rdalen/Boxify/KiCad/templates/Panel PCB w23.5x23.5mm/meta/panel.png

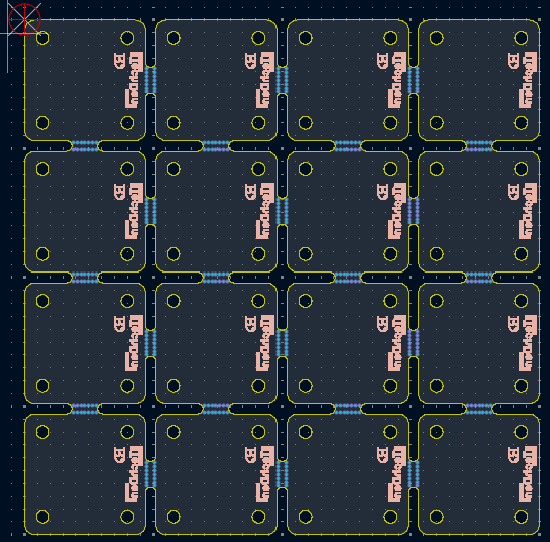
KiCad/templates/Panel PCB w23.5x23.5mm/meta/panel.png
