rdalen/Boxify/KiCad/templates/Panel PCB w23.5x49mm/meta/panel.png

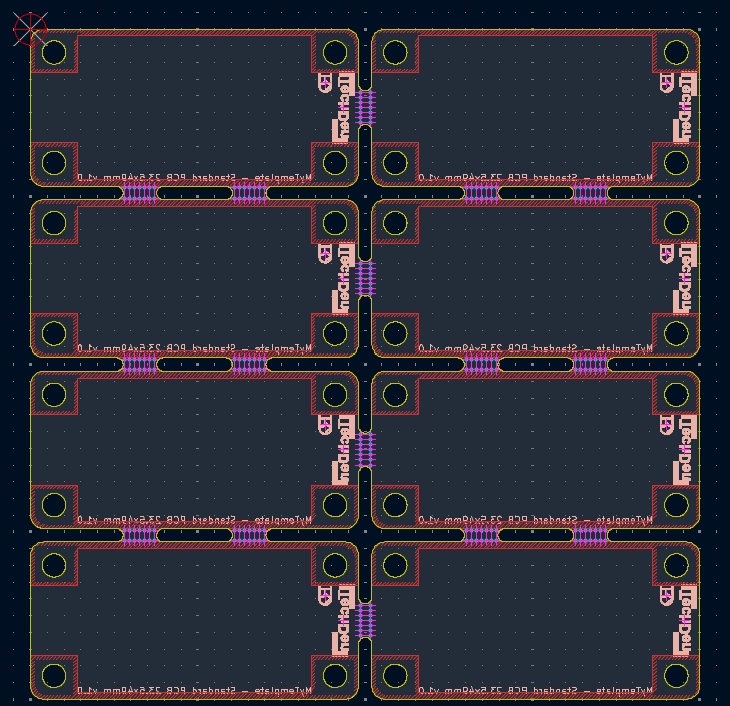
KiCad/templates/Panel PCB w23.5x49mm/meta/panel.png
