rdalen/Boxify/KiCad/templates/Panel PCB w49x49mm/meta/panel.png

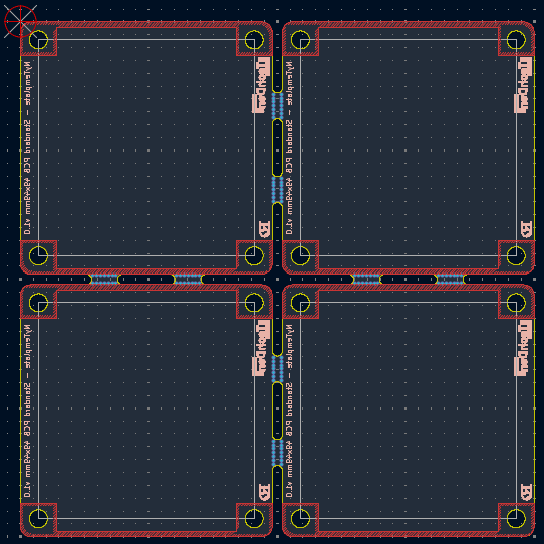
KiCad/templates/Panel PCB w49x49mm/meta/panel.png
