rdalen/Boxify/KiCad/templates/Panel PCB w100x100mm/meta/brd.png

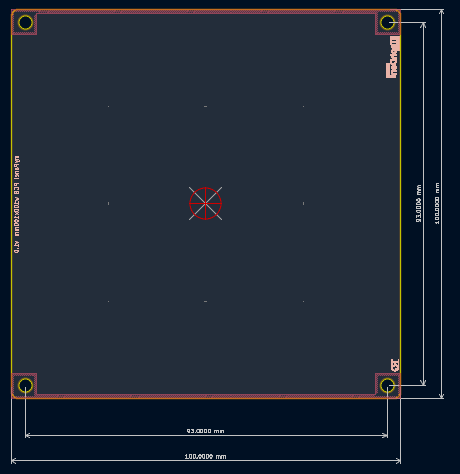
KiCad/templates/Panel PCB w100x100mm/meta/brd.png
