rdalen/Boxify/KiCad/templates/Prototype PCB w30x70mm/meta/brd.png

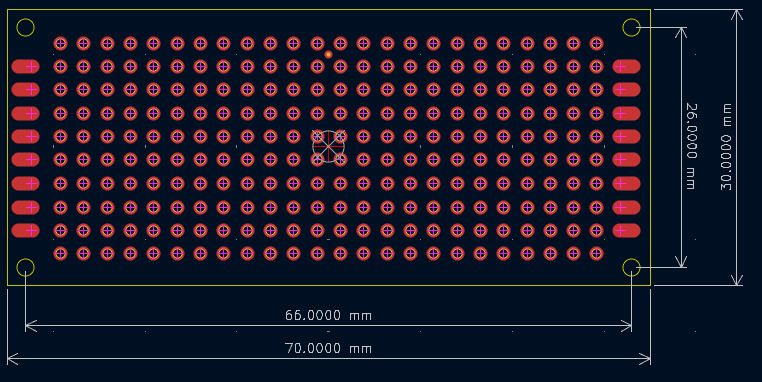
KiCad/templates/Prototype PCB w30x70mm/meta/brd.png
