rdalen/Boxify/KiCad/templates/Prototype PCB w60x80mm/meta/brd.png

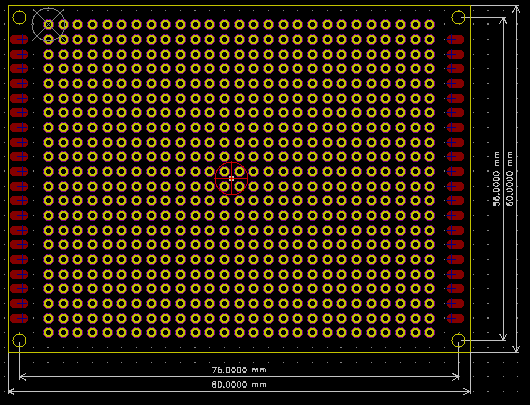
KiCad/templates/Prototype PCB w60x80mm/meta/brd.png
