rdalen/Boxify/KiCad/templates/Prototype PCB w70x90mm/meta/brd.png

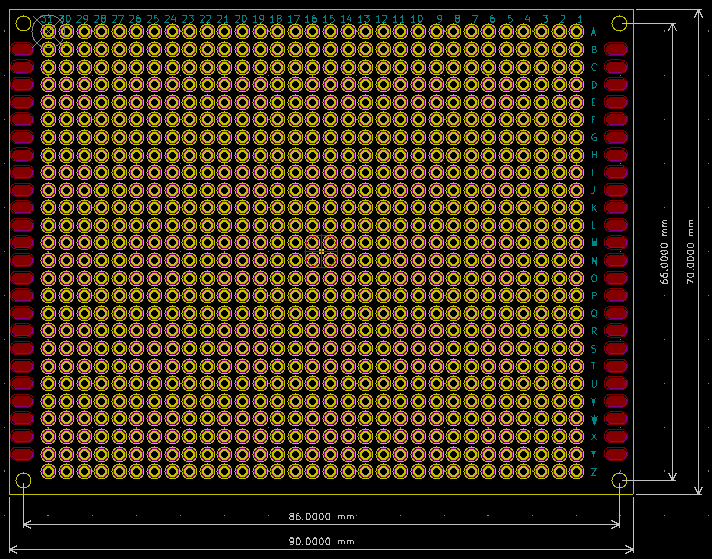
KiCad/templates/Prototype PCB w70x90mm/meta/brd.png
